zeeeeeb/ErgoDoxHotSwap/ErgoDox Acrylic Case/ErgoDOX Acrylic Case - Designed by Litster/with Wrist Rest/Left/ErgoDOX Case Layer 1 Top - Left.dxf

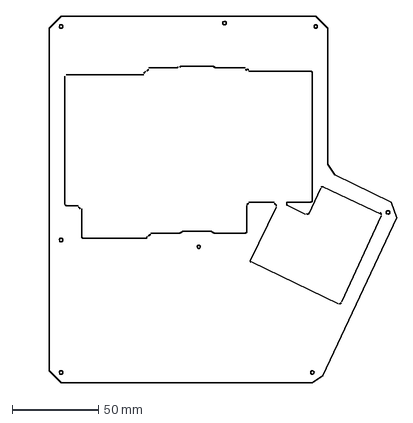
[picture p15: CAD file, 2018-05-15]
ErgoDox Acrylic Case/ErgoDOX Acrylic Case - Designed by Litster/with Wrist Rest/Left/ErgoDOX Case Layer 1 Top - Left.dxf
221.0 x 213.0 mm
