zeeeeeb/ErgoDoxHotSwap/ErgoDox Acrylic Case/ErgoDOX Acrylic Case - Designed by Litster/with Wrist Rest/Right/ErgoDOX Wrist Rest Case Layer 3 Plate - Right.dxf

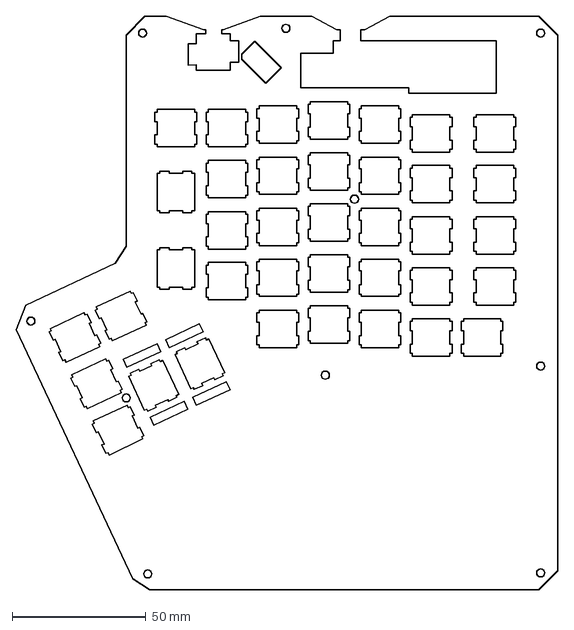
[picture p16: CAD file, 2018-10-16]
ErgoDox Acrylic Case/ErgoDOX Acrylic Case - Designed by Litster/with Wrist Rest/Right/ErgoDOX Wrist Rest Case Layer 3 Plate - Right.dxf
202.0 x 214.1 mm
