zeeeeeb/ErgoDoxHotSwap/ErgoDox Acrylic Case/ErgoDOX Acrylic Case - Designed by Litster/Standard/Left/ErgoDOX Case Layer 1 Top - Left.dxf

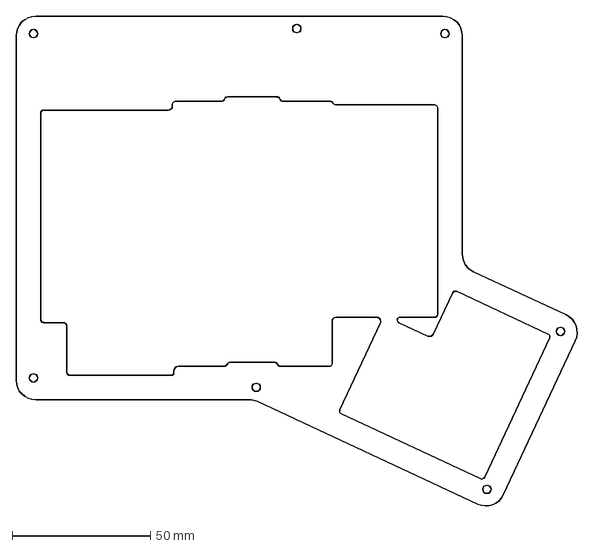
[picture p17: CAD file, 2018-09-24]
ErgoDox Acrylic Case/ErgoDOX Acrylic Case - Designed by Litster/Standard/Left/ErgoDOX Case Layer 1 Top - Left.dxf
202.8 x 177.8 mm
