zeeeeeb/ErgoDoxHotSwap/ErgoDox Acrylic Case/ErgoDOX Acrylic Case - Designed by Litster/Standard/Right/ErgoDOX Case Layer 2 Spacer - Right.dxf

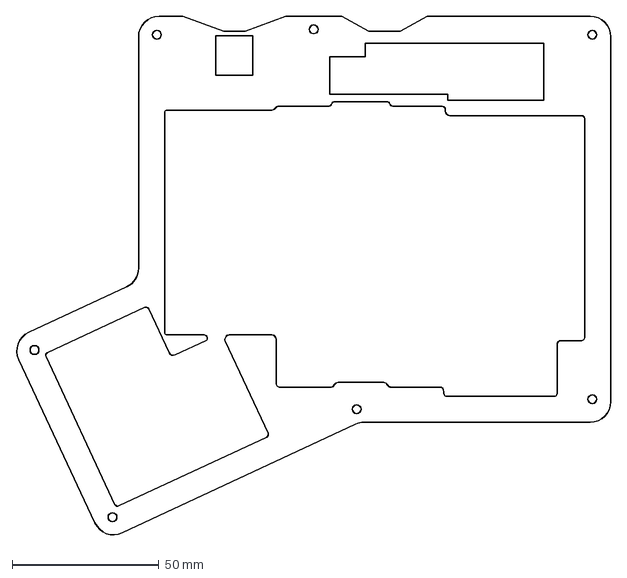
[picture p18: CAD file, 2018-10-16]
ErgoDox Acrylic Case/ErgoDOX Acrylic Case - Designed by Litster/Standard/Right/ErgoDOX Case Layer 2 Spacer - Right.dxf
202.8 x 177.8 mm
