zeeeeeb/ErgoDoxHotSwap/ErgoDox Acrylic Case/ErgoDOX Acrylic Case - Designed by Litster/with Wrist Rest/Left/ErgoDOX Case Layer 4 Spacer - Left.dxf

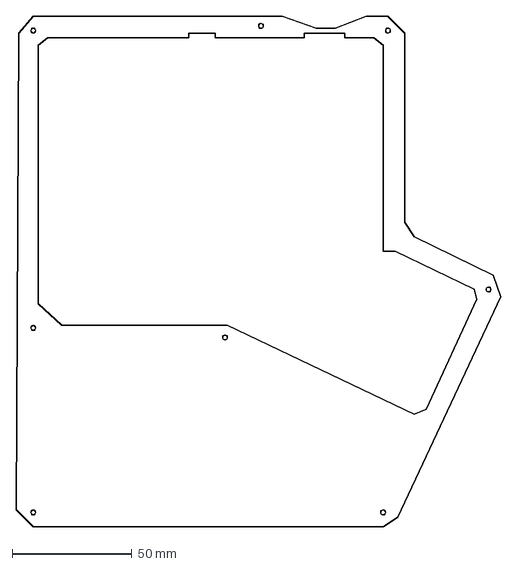
[picture p19: CAD file, 2018-05-15]
ErgoDox Acrylic Case/ErgoDOX Acrylic Case - Designed by Litster/with Wrist Rest/Left/ErgoDOX Case Layer 4 Spacer - Left.dxf
202.0 x 213.0 mm
