zeeeeeb/ErgoDoxHotSwap/ErgoDox Acrylic Case/ErgoDOX Acrylic Case - Designed by Litster/with Wrist Rest/Right/ErgoDOX Wrist Rest Case Layer 5 Bottom - Right.dxf

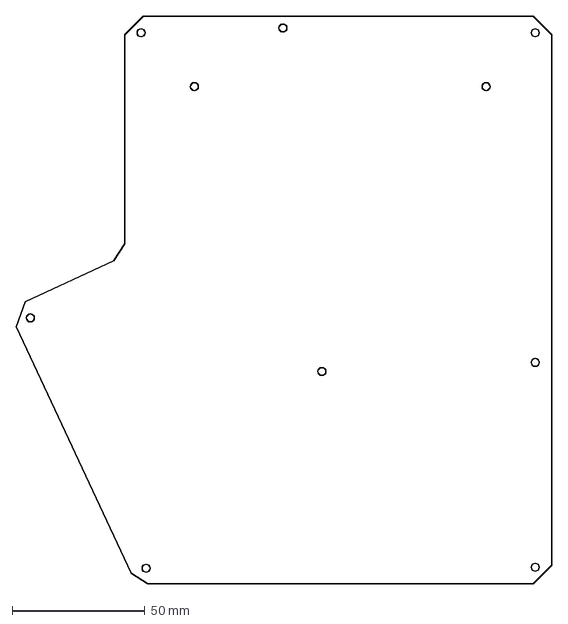
[picture p20: CAD file, 2018-10-16]
ErgoDox Acrylic Case/ErgoDOX Acrylic Case - Designed by Litster/with Wrist Rest/Right/ErgoDOX Wrist Rest Case Layer 5 Bottom - Right.dxf
202.0 x 214.1 mm
